Simbashrek276/MonkiiBoard_Keyboards/Medias/MonkiiBoard39/MonkiiBoard39_halfview.jpg

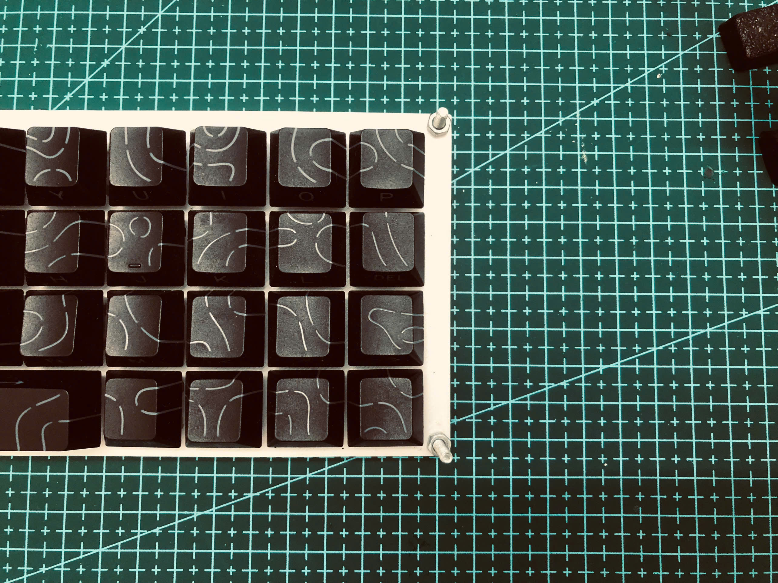
Medias/MonkiiBoard39/MonkiiBoard39_halfview.jpg
