Simbashrek276/MonkiiBoard_Keyboards/Medias/MonkiiBoard39/MonkiiBoard39_lensview.jpg

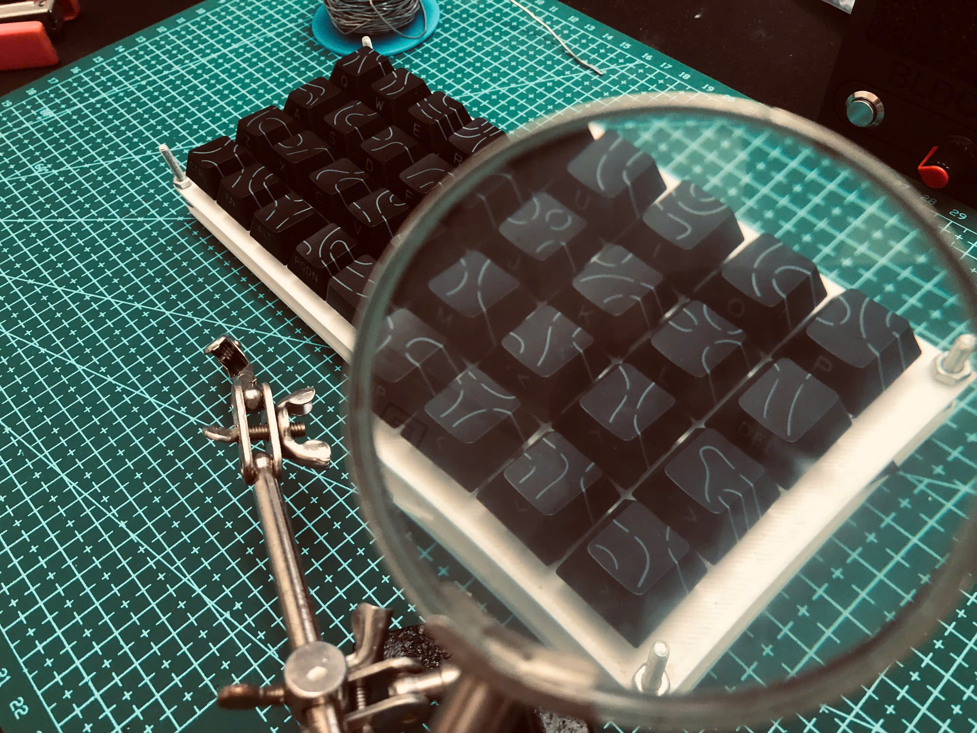
Medias/MonkiiBoard39/MonkiiBoard39_lensview.jpg
