Simbashrek276/MonkiiBoard_Keyboards/Medias/MonkiiBoard39/MonkiiBoard39_shadow.png

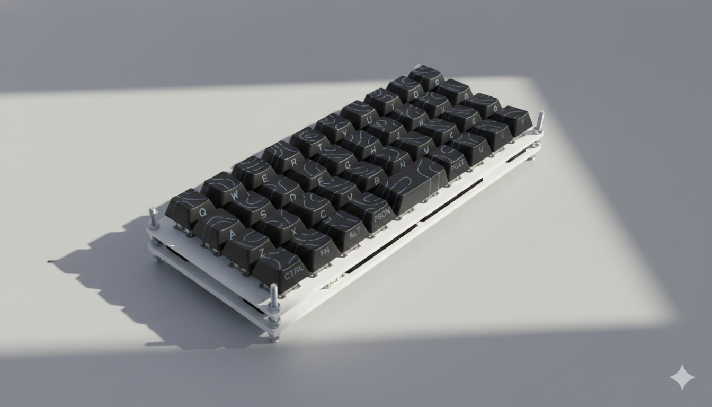
Medias/MonkiiBoard39/MonkiiBoard39_shadow.png
