Simbashrek276/MonkiiBoard_Keyboards/Medias/MonkiiPad3x3/MonkiiPad3x3_inside_upper.jpg

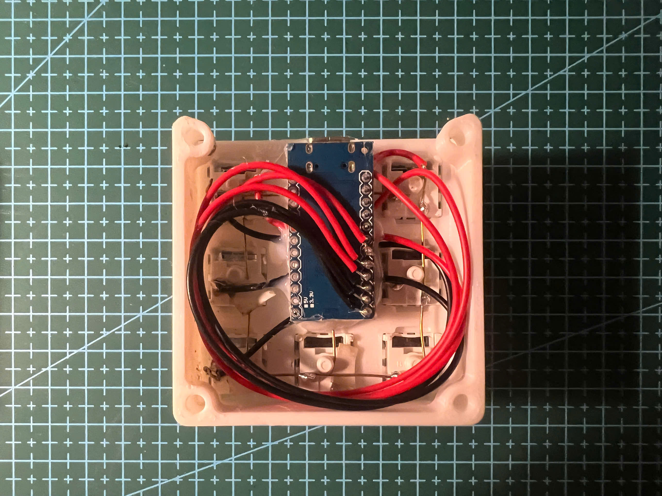
Medias/MonkiiPad3x3/MonkiiPad3x3_inside_upper.jpg
