Simbashrek276/MonkiiBoard_Keyboards/Medias/MonkiiPad20/MonkiiPad20_portrait.jpg

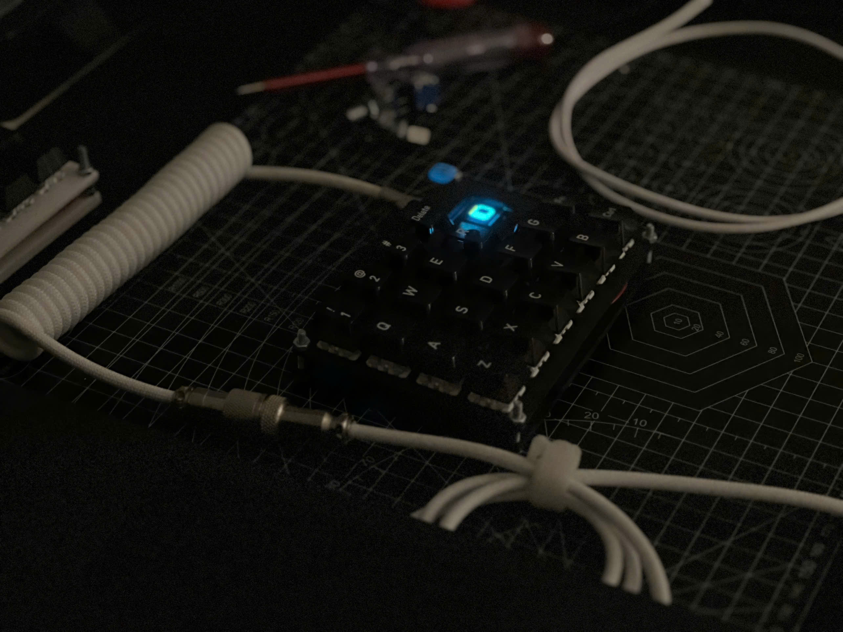
Medias/MonkiiPad20/MonkiiPad20_portrait.jpg
