Simbashrek276/MonkiiBoard_Keyboards/Medias/MonkiiPad20/MonkiiPad20_rotated_90.jpg

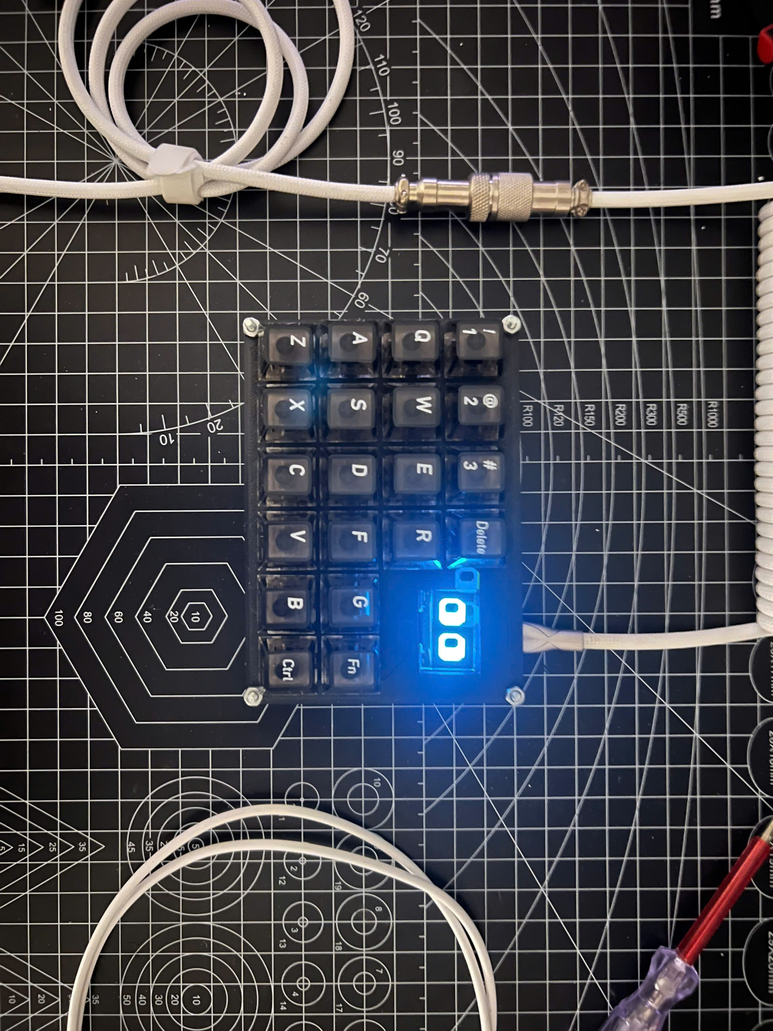
Medias/MonkiiPad20/MonkiiPad20_rotated_90.jpg
